Ubantu011w/Parking-Radar-Application/img/DSC_1428.JPG

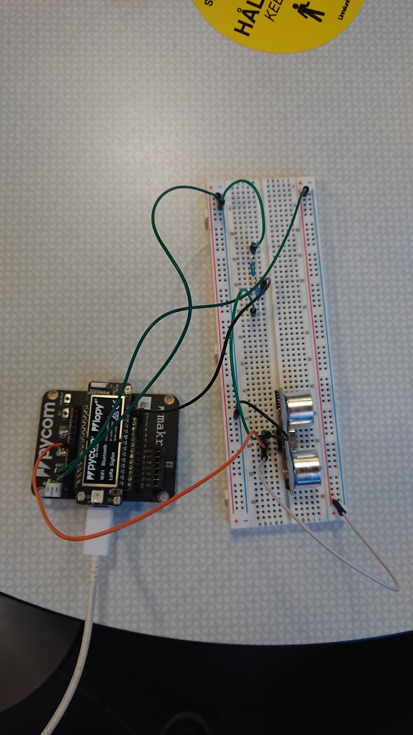
img/DSC_1428.JPG
