Ubantu011w/Parking-Radar-Application/img/DSC_1432.JPG

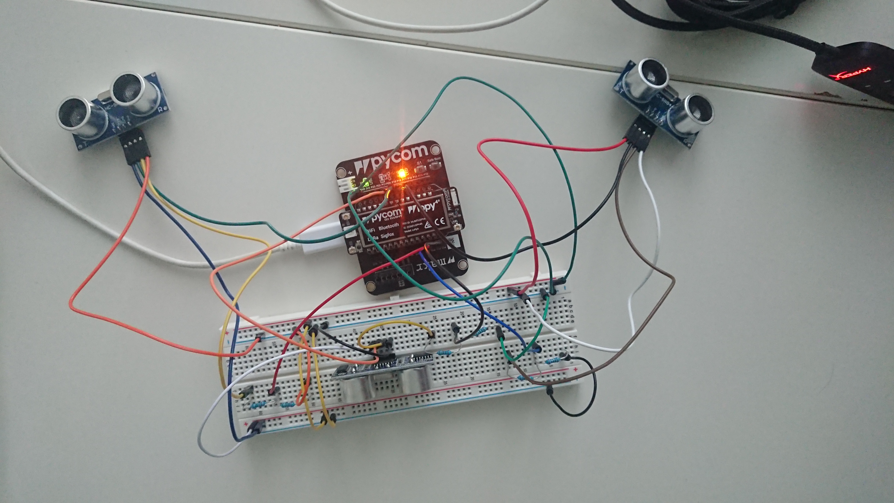
img/DSC_1432.JPG
